robgmsn/PureDigit/examples/VCO/VCO.ino

/*
  GMSN! Pure Digit
  28th July 2018
  cc-by 4.0
  Rob Spencer

  VCO
  Yes!! Huge personal technological breakthrough!! Timer controlled writes to the DAC.
  It started off with 44kHz sample rate,. but this had to be reduced so the other processing in the main loop could run.
  It's now down to 15kHz with no real impact on the quality. This is just a tiny module to learn SMD soldering,
  so I'm pretty happy with the result. Obviously things would be pretty different with a fast DSP chip through 16bit DACs :)
  The frequency runs from about 10Hz, up to just over 2Khz, so plenty of subbass and bass goodness to play with.

  Encoder controls the frequency.
  Push and turn to change the waveform: Sine & Saw. Should really add Square too....
*/

#include <PureDigit.h>

PureDigit digit;
int waveForm = 2, freqEnc = 800, cyclePhase = 1, val, cvIn, cvInFreq, freq; //11.53Hz
float ptr = 0, inc = 1;
int sineTable[512] = {2048, 2054, 2060, 2066, 2073, 2079, 2085, 2091, 2098, 2104, 2110, 2117, 2123, 2129, 2135, 2142,
                      2148, 2154, 2161, 2167, 2173, 2179, 2186, 2192, 2198, 2204, 2211, 2217, 2223, 2229, 2236, 2242,
                      2248, 2254, 2261, 2267, 2273, 2279, 2286, 2292, 2298, 2304, 2311, 2317, 2323, 2329, 2335, 2342,
                      2348, 2354, 2360, 2367, 2373, 2379, 2385, 2391, 2398, 2404, 2410, 2416, 2422, 2428, 2435, 2441,
                      2447, 2453, 2459, 2465, 2472, 2478, 2484, 2490, 2496, 2502, 2508, 2514, 2521, 2527, 2533, 2539,
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
  TCCR1B |= (1 << CS10);    // 1 prescaler
  TIMSK1 |= (1 << OCIE1A);  // enable timer compare interrupt
  interrupts();             // enable all interrupts

}

ISR(TIMER1_COMPA_vect)          // timer compare interrupt service routine
{
  switch (waveForm) {
    case 1: //sine

      switch (cyclePhase) {
        case 1:
          ptr = ptr + inc;
          if (ptr > 512) {
            ptr = 512 - (ptr - 512);
            cyclePhase = 2;
          }
          val = sineTable[int(ptr)];
          break;
        case 2:
          ptr = ptr - inc;
          if (ptr < 1) {
            ptr = abs(ptr);
            val = sineTable[int(ptr)];
            val = 2048 - (val - 2048);
            cyclePhase = 3;
          } else {
            val = sineTable[int(ptr)];
          }
          break;
        case 3:
          ptr = ptr + inc;
          if (ptr > 512) {
            ptr = 512 - (ptr - 512);
            cyclePhase = 4;
          }
          val = sineTable[int(ptr)];
          val = 2048 - (val - 2048);
          break;
        case 4:
          ptr = ptr - inc;
          if (ptr < 1) {
            ptr = abs(ptr);
            val = sineTable[int(ptr)];
            cyclePhase = 1;
          } else {
            val = sineTable[int(ptr)];
            val = 2048 - (val - 2048);
          }
          break;
      }
      break;

    case 2: //saw
      ptr = ptr - (inc * 2.0);
      if (ptr < 1) {
        ptr = 4096;
      }
      val = abs(ptr);
      break;
  }
  digit.dacWrite(val);
  cvIn = digit.adcRead(1);


}

void loop() {
  if (digit.getSwitchState() == 0) {
    freqEnc = digit.encodeVal(freqEnc);
    digit.displayLED(freqEnc, 2, 0);
  } else {
    waveForm = digit.encodeVal(waveForm);
    waveForm = constrain(waveForm, 1, 2);
    digit.displayLED(waveForm, 1, 0);
  }

  //noInterrupts();
  //interrupts();
  //freqEnc = constrain(freqEnc, 1, 800);
  //cvInFreq = 4096 - (cvIn - 4096);
  cvInFreq = map(cvIn, 0, 4096, 800, 0);
  freq =  cvInFreq + (freqEnc-1000);
  inc = fscale( 0, 800, 1, 200, freq, -4);


  //cvInFreq = map(cvIn, 0, 4096, 1, 800);



}
